PotatoDotJar/iot-window-actuator/MechanicalDesigns/20190813_112354.jpg

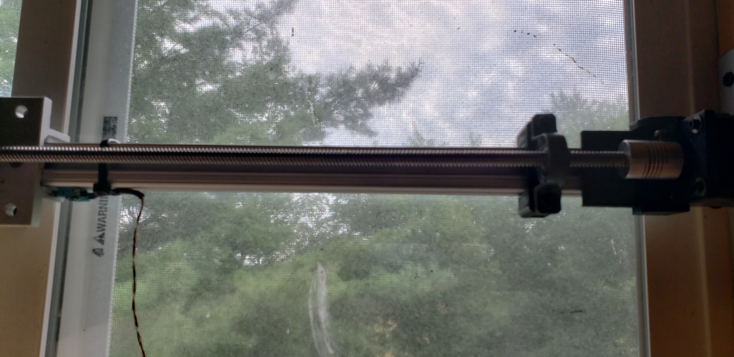
MechanicalDesigns/20190813_112354.jpg
