PotatoDotJar/iot-window-actuator/MechanicalDesigns/20190813_112356.jpg

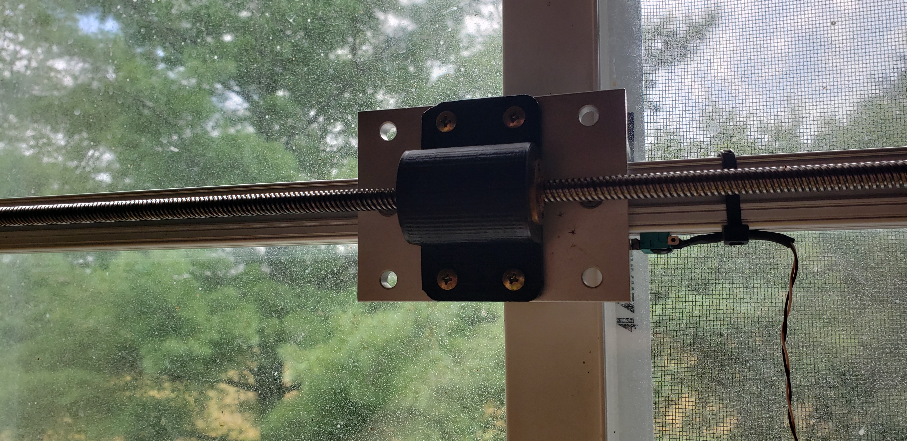
MechanicalDesigns/20190813_112356.jpg
