PotatoDotJar/iot-window-actuator/MechanicalDesigns/20190813_112401.jpg

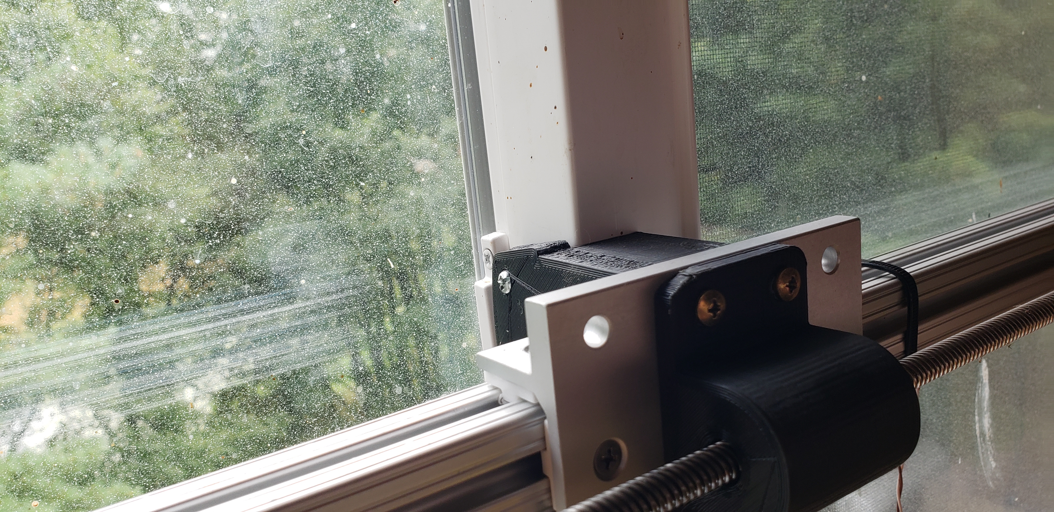
MechanicalDesigns/20190813_112401.jpg
